aarontodd82/GenesisEngine/src/GenesisEngine.cpp

#include "GenesisEngine.h"

// =============================================================================
// Timing Constants
// VGM sample rate is 44100 Hz
// Microseconds per sample = 1000000 / 44100 = 22.675736961...
//
// For integer math, we use: samples = (elapsed_micros * 441) / 10000
// This gives us exact timing with no floating point
// =============================================================================

// =============================================================================
// Constructor
// =============================================================================

GenesisEngine::GenesisEngine(GenesisBoard& board)
  : board_(board),
    parser_(board),
    state_(GenesisEngineState::STOPPED),
    looping_(false),
    currentSample_(0),
    waitSamples_(0),
    playbackStartTime_(0),
    samplesPlayed_(0)
{
  // PCM data for DAC playback is now handled dynamically by PCMDataBank
  // inside VGMParser - no pre-allocated buffer needed
}

// =============================================================================
// Playback Control
// =============================================================================

bool GenesisEngine::play(const uint8_t* data, size_t length) {
  // Stop any current playback
  stop();

  // Set up PROGMEM source
  progmemSource_.setData(data, length);

  if (!progmemSource_.open()) {
    GENESIS_DEBUG_PRINTLN("Failed to open PROGMEM source");
    return false;
  }

  parser_.setSource(&progmemSource_);

  bool success = startPlayback();

  // After parsing header, set data start offset so seek positions are relative
  if (success) {
    progmemSource_.setDataStart(parser_.getDataOffset());
  }

  return success;
}

bool GenesisEngine::playChunked(const uint8_t* const* chunks, const uint16_t* chunkSizes,
                                 uint8_t numChunks, uint32_t totalLength) {
  // Stop any current playback
  stop();

  // Set up chunked PROGMEM source
  chunkedProgmemSource_.setData(chunks, chunkSizes, numChunks, totalLength);

  if (!chunkedProgmemSource_.open()) {
    GENESIS_DEBUG_PRINTLN("Failed to open chunked PROGMEM source");
    return false;
  }

  parser_.setSource(&chunkedProgmemSource_);

  bool success = startPlayback();

  // After parsing header, set data start offset so seek positions are relative
  if (success) {
    chunkedProgmemSource_.setDataStart(parser_.getDataOffset());
  }

  return success;
}

bool GenesisEngine::startPlayback() {
  // Parse header
  if (!parser_.parseHeader()) {
    GENESIS_DEBUG_PRINTLN("Failed to parse VGM header");
    state_ = GenesisEngineState::STOPPED;
    return false;
  }

  // Reset timing
  currentSample_ = 0;
  waitSamples_ = 0;
  samplesPlayed_ = 0;
  playbackStartTime_ = micros();

  // Reset hardware
  board_.muteAll();

  // Start playing
  state_ = GenesisEngineState::PLAYING;

  GENESIS_DEBUG_PRINTLN("Playback started");
  return true;
}

void GenesisEngine::stop() {
  if (state_ == GenesisEngineState::STOPPED) {
    return;
  }

  // Full hardware reset to clear any hanging notes
  board_.reset();

  // Reset state
  parser_.reset();
  state_ = GenesisEngineState::STOPPED;
  currentSample_ = 0;
  waitSamples_ = 0;

  GENESIS_DEBUG_PRINTLN("Playback stopped");
}

void GenesisEngine::pause() {
  if (state_ == GenesisEngineState::PLAYING) {
    state_ = GenesisEngineState::PAUSED;
    board_.muteAll();
    GENESIS_DEBUG_PRINTLN("Playback paused");
  }
}

void GenesisEngine::resume() {
  if (state_ == GenesisEngineState::PAUSED) {
    state_ = GenesisEngineState::PLAYING;
    // Adjust start time so timing continues correctly
    // We pretend playback started (now - time_already_played)
    uint32_t elapsedSamplesMicros = (samplesPlayed_ * 10000UL) / 441UL;
    playbackStartTime_ = micros() - elapsedSamplesMicros;
    GENESIS_DEBUG_PRINTLN("Playback resumed");
  }
}

// =============================================================================
// Update
// =============================================================================

void GenesisEngine::update() {
  if (state_ != GenesisEngineState::PLAYING) {
    return;
  }

  uint32_t now = micros();
  uint32_t elapsed = now - playbackStartTime_;

  // Handle micros() overflow (happens every ~70 minutes)
  // If elapsed is huge, assume overflow occurred
  if (elapsed > 0x80000000UL) {
    // Overflow - reset timing base
    playbackStartTime_ = now;
    elapsed = 0;
    // Keep samplesPlayed_ as-is to maintain position
  }

  // Calculate how many samples should have played by now
  // samples = elapsed_micros * 44100 / 1000000 = elapsed_micros * 441 / 10000
  uint32_t targetSamples = (elapsed / 10000UL) * 441UL + ((elapsed % 10000UL) * 441UL) / 10000UL;

  // Process commands until we catch up
  while (samplesPlayed_ < targetSamples) {
    // If we have pending wait samples, consume them
    if (waitSamples_ > 0) {
      uint32_t samplesToAdvance = targetSamples - samplesPlayed_;
      if (samplesToAdvance > waitSamples_) {
        samplesToAdvance = waitSamples_;
      }

      waitSamples_ -= samplesToAdvance;
      samplesPlayed_ += samplesToAdvance;
      currentSample_ += samplesToAdvance;

      if (waitSamples_ > 0) {
        // Still waiting, done for now
        return;
      }
    }

    // Process commands until next wait
    processCommands();

    if (state_ != GenesisEngineState::PLAYING) {
      // Playback ended
      return;
    }
  }
}

void GenesisEngine::processCommands() {
  // Process VGM commands until a wait is encountered
  waitSamples_ = parser_.processUntilWait();

  if (parser_.isFinished()) {
    // End of file reached
    if (looping_ && parser_.hasLoop()) {
      // Seek to loop point
      if (parser_.seekToLoop()) {
        GENESIS_DEBUG_PRINTLN("Looping");
        waitSamples_ = parser_.processUntilWait();
        return;
      }
    }

    // Playback finished - full reset to clear any hanging notes
    board_.reset();
    state_ = GenesisEngineState::FINISHED;
    GENESIS_DEBUG_PRINTLN("Playback finished");
  }
}

// =============================================================================
// SD Card Playback
// =============================================================================

#if GENESIS_ENGINE_USE_SD
bool GenesisEngine::playFile(const char* path) {
  // Stop any current playback
  stop();

  // Check file extension
  size_t len = strlen(path);
  bool isVGZ = false;
  if (len >= 4) {
    const char* ext = path + len - 4;
    isVGZ = (strcasecmp(ext, ".vgz") == 0);
  }

#if GENESIS_ENGINE_USE_VGZ
  // Use VGZSource for VGZ files (streaming decompression)
  if (isVGZ) {
    if (!vgzSource_.openFile(path)) {
      GENESIS_DEBUG_PRINT("Failed to open VGZ: ");
      GENESIS_DEBUG_PRINTLN(path);
      return false;
    }

    if (!vgzSource_.open()) {
      GENESIS_DEBUG_PRINTLN("Failed to prepare VGZ source");
      return false;
    }

    parser_.setSource(&vgzSource_);
    bool success = startPlayback();

    // After parsing header, notify VGZSource that we've reached data start
    // This resets currentDataPos_ to 0, so positions are relative to data start
    if (success) {
      vgzSource_.setDataStart();

      // Set loop offset relative to data start (VGMParser now calculates this)
      if (parser_.hasLoop()) {
        vgzSource_.setLoopOffset(parser_.getLoopOffsetInData());
      }
    }

    return success;
  }
#else
  // VGZ not supported on this platform
  if (isVGZ) {
    Serial.println("VGZ files not supported on this platform");
    Serial.println("Use vgm_prep.py to convert:");
    Serial.println("  python vgm_prep.py song.vgz -o song.vgm");
    return false;
  }
#endif

  // Use SDSource for VGM files (direct streaming)
  if (!sdSource_.openFile(path)) {
    GENESIS_DEBUG_PRINT("Failed to open: ");
    GENESIS_DEBUG_PRINTLN(path);
    return false;
  }

  if (!sdSource_.open()) {
    GENESIS_DEBUG_PRINTLN("Failed to prepare SD source");
    return false;
  }

  parser_.setSource(&sdSource_);
  bool success = startPlayback();

  // After parsing header, set data start offset so seek positions are relative
  if (success) {
    sdSource_.setDataStart(parser_.getDataOffset());
  }

  return success;
}
#endif // GENESIS_ENGINE_USE_SD
