aarontodd82/GenesisEngine/examples/MIDISynth/MIDISynth.ino

/**
 * MIDISynth - MIDI Synthesizer for GenesisEngine
 *
 * Turns the GenesisEngine hardware into a MIDI synthesizer.
 *
 * MIDI Channel Mapping:
 *   Ch 1-6:  YM2612 FM channels 1-6
 *   Ch 7-9:  SN76489 PSG tone channels 1-3
 *   Ch 10:   SN76489 PSG noise channel
 *
 * Supported Platforms:
 *   - Teensy 4.x: USB MIDI (set USB Type to "Serial + MIDI")
 *   - Arduino Uno/Mega: Serial MIDI via companion app
 *   - Any board: Serial MIDI at 115200 baud
 *
 * Both USB MIDI and Serial MIDI can be used simultaneously on Teensy.
 */

// =============================================================================
// Platform Detection
// =============================================================================

// Detect if USB MIDI is available (Teensy with MIDI enabled)
#if defined(USBCON) && defined(TEENSYDUINO)
    #define HAS_USB_MIDI 1
#else
    #define HAS_USB_MIDI 0
#endif

// Firmware version for identification
#define FIRMWARE_VERSION 1

#include <GenesisBoard.h>
#include <synth/FMPatch.h>
#include <synth/FMFrequency.h>
#include <synth/PSGFrequency.h>
#include <synth/PSGEnvelope.h>
#include <synth/DefaultPatches.h>

// =============================================================================
// Pin Configuration (platform specific)
// =============================================================================

#ifdef ARDUINO_ARCH_ESP32
  const uint8_t PIN_WR_P = 16;  // WR_P - SN76489 (PSG) write strobe
  const uint8_t PIN_WR_Y = 17;  // WR_Y - YM2612 write strobe
  const uint8_t PIN_IC_Y = 25;  // IC_Y - YM2612 reset
  const uint8_t PIN_A0_Y = 26;  // A0_Y - YM2612 address bit 0
  const uint8_t PIN_A1_Y = 27;  // A1_Y - YM2612 address bit 1 (port select)
  const uint8_t PIN_SCK  = 18;  // SCK  - Hardware SPI (fixed on ESP32)
  const uint8_t PIN_SDI  = 23;  // SDI  - Hardware SPI (fixed on ESP32)
#else
  // Teensy / Arduino defaults
  const uint8_t PIN_WR_P = 2;   // WR_P - SN76489 (PSG) write strobe
  const uint8_t PIN_WR_Y = 3;   // WR_Y - YM2612 write strobe
  const uint8_t PIN_IC_Y = 4;   // IC_Y - YM2612 reset
  const uint8_t PIN_A0_Y = 5;   // A0_Y - YM2612 address bit 0
  const uint8_t PIN_A1_Y = 6;   // A1_Y - YM2612 address bit 1 (port select)
  const uint8_t PIN_SCK  = 13;  // SCK  - Shift register clock (ignored w/ HW SPI)
  const uint8_t PIN_SDI  = 11;  // SDI  - Shift register data (ignored w/ HW SPI)
#endif

GenesisBoard board(PIN_WR_P, PIN_WR_Y, PIN_IC_Y, PIN_A0_Y, PIN_A1_Y, PIN_SCK, PIN_SDI);

// =============================================================================
// Patch Storage
// =============================================================================

// RAM storage for user-loaded patches
FMPatch fmPatches[16];           // 16 FM patch slots
PSGEnvelope psgEnvelopes[8];     // 8 PSG envelope slots

// Current patch assignment per channel
uint8_t fmChannelPatch[6] = {0, 1, 2, 3, 4, 5};
uint8_t psgChannelEnv[4] = {0, 1, 2, 3};  // Each PSG channel gets different envelope

// =============================================================================
// PSG Envelope State (software envelopes at 60Hz)
// =============================================================================

struct PSGChannelState {
    bool active;
    bool noteOn;
    uint8_t envPos;
    uint16_t baseTone;
    uint8_t baseNote;
};

PSGChannelState psgState[4] = {0};

// =============================================================================
// Synth Mode
// =============================================================================

enum SynthMode {
    MODE_MULTI,      // 6 independent FM channels (Ch 1-6), each with own patch
    MODE_POLY6       // 6-voice polyphonic on Ch 1, all same patch
};

SynthMode synthMode = MODE_MULTI;
uint8_t polyPatchSlot = 0;  // Patch slot used in poly mode

// =============================================================================
// FM Channel/Voice State
// =============================================================================

struct FMChannelState {
    bool noteOn;
    bool sustainPending;  // Note should release when sustain pedal is lifted
    uint8_t currentNote;
    uint8_t velocity;
    uint32_t timestamp;  // For voice stealing (when note started)
};

FMChannelState fmState[6] = {0};

// Sustain pedal state per channel (for multi mode) or global (for poly mode)
bool sustainPedal[16] = {false};

// Pitch bend per FM channel (-8192 to +8191)
// In poly mode, all voices share the pitch bend from channel 0
int16_t fmPitchBend[6] = {0, 0, 0, 0, 0, 0};

// =============================================================================
// Timing
// =============================================================================

uint32_t lastEnvTick = 0;
const uint32_t ENV_TICK_US = 16667;  // 60Hz = 16667 microseconds

// =============================================================================
// Forward Declarations
// =============================================================================

void setFMFrequencyWithBend(uint8_t ch, uint8_t note, int16_t bend);
void fmNoteOn(uint8_t ch, uint8_t note, uint8_t velocity);
void fmNoteOff(uint8_t ch, uint8_t note);
void fmKeyOff(uint8_t ch);
void writeFMPatch(uint8_t ch, const FMPatch& patch);
void processSerialMIDI();
void handleSerialMIDIByte(uint8_t byte);

// =============================================================================
// Serial MIDI Parser State
// =============================================================================

// MIDI message types for parsing
#define MIDI_NOTE_OFF       0x80
#define MIDI_NOTE_ON        0x90
#define MIDI_POLY_PRESSURE  0xA0
#define MIDI_CONTROL_CHANGE 0xB0
#define MIDI_PROGRAM_CHANGE 0xC0
#define MIDI_CHAN_PRESSURE  0xD0
#define MIDI_PITCH_BEND     0xE0
#define MIDI_SYSEX_START    0xF0
#define MIDI_SYSEX_END      0xF7

// Serial MIDI parser state
uint8_t serialMidiBuffer[128];   // Buffer for incoming MIDI data
uint8_t serialMidiPos = 0;       // Current position in buffer
uint8_t serialMidiExpected = 0;  // Expected message length
uint8_t serialMidiStatus = 0;    // Running status byte
bool serialInSysEx = false;      // Currently receiving SysEx

// =============================================================================
// Voice Allocator (for Poly Mode)
// =============================================================================

/**
 * Find a voice to use for a new note.
 * Strategy:
 *   1. Reuse voice if same note is retriggered
 *   2. Use first free voice
 *   3. Steal oldest voice (voice stealing)
 */
int8_t allocateVoice(uint8_t note) {
    // 1. Check if this note is already playing (retrigger - reuse same voice)
    for (int i = 0; i < 6; i++) {
        if (fmState[i].noteOn && fmState[i].currentNote == note) {
            return i;
        }
    }

    // 2. Find first free voice
    for (int i = 0; i < 6; i++) {
        if (!fmState[i].noteOn) {
            return i;
        }
    }

    // 3. All voices busy - steal oldest note
    uint32_t oldest = UINT32_MAX;
    int8_t oldestIdx = 0;
    for (int i = 0; i < 6; i++) {
        if (fmState[i].timestamp < oldest) {
            oldest = fmState[i].timestamp;
            oldestIdx = i;
        }
    }

    // Release the stolen voice before reusing
    fmKeyOff(oldestIdx);

    return oldestIdx;
}

/**
 * Find the voice playing a specific note (for note-off).
 * If multiple voices play same note, returns the oldest one (FIFO release).
 * Returns -1 if note not found.
 */
int8_t findVoiceByNote(uint8_t note) {
    int8_t found = -1;
    uint32_t oldest = UINT32_MAX;

    for (int i = 0; i < 6; i++) {
        if (fmState[i].noteOn && fmState[i].currentNote == note) {
            if (fmState[i].timestamp < oldest) {
                oldest = fmState[i].timestamp;
                found = i;
            }
        }
    }
    return found;
}

/**
 * Switch to poly mode - load same patch on all 6 FM channels
 */
void enablePolyMode(uint8_t patchSlot) {
    synthMode = MODE_POLY6;
    polyPatchSlot = patchSlot;

    // Load the same patch on all 6 channels
    for (uint8_t ch = 0; ch < 6; ch++) {
        fmChannelPatch[ch] = patchSlot;  // All channels use same patch
        writeFMPatch(ch, fmPatches[patchSlot]);
        fmState[ch].noteOn = false;
    }

    Serial.print("Poly mode enabled, patch slot ");
    Serial.println(patchSlot);
}

/**
 * Switch to multi-timbral mode - restore individual patches per channel
 */
void enableMultiMode() {
    synthMode = MODE_MULTI;

    // Restore individual patches per channel
    for (uint8_t ch = 0; ch < 6; ch++) {
        writeFMPatch(ch, fmPatches[fmChannelPatch[ch]]);
        fmState[ch].noteOn = false;
    }

    Serial.println("Multi mode enabled");
}

// =============================================================================
// Setup
// =============================================================================

void setup() {
    Serial.begin(115200);

    board.begin();
    board.reset();

    // Load default patches from PROGMEM
    loadDefaultPatches();

    // Initialize all FM channels with their assigned patches
    for (uint8_t ch = 0; ch < 6; ch++) {
        writeFMPatch(ch, fmPatches[fmChannelPatch[ch]]);
        // Set stereo output (both L+R enabled)
        setFMPanning(ch, 0xC0);  // Both speakers
    }

    // Silence PSG
    board.silencePSG();

    Serial.println("MIDISynth ready");
}

// =============================================================================
// Main Loop
// =============================================================================

void loop() {
    // Process USB MIDI from computer (Teensy only)
    #if HAS_USB_MIDI
    while (usbMIDI.read()) {
        // Convert usbMIDI type to our unified type constants
        uint8_t type = usbMIDI.getType();
        uint8_t unifiedType;
        switch (type) {
            case usbMIDI.NoteOff:         unifiedType = TYPE_NOTE_OFF; break;
            case usbMIDI.NoteOn:          unifiedType = TYPE_NOTE_ON; break;
            case usbMIDI.ControlChange:   unifiedType = TYPE_CONTROL_CHANGE; break;
            case usbMIDI.ProgramChange:   unifiedType = TYPE_PROGRAM_CHANGE; break;
            case usbMIDI.PitchBend:       unifiedType = TYPE_PITCH_BEND; break;
            case usbMIDI.SystemExclusive: unifiedType = TYPE_SYSEX; break;
            default: continue;  // Skip unknown types
        }
        handleMIDI(
            unifiedType,
            usbMIDI.getChannel() - 1,  // Convert to 0-indexed
            usbMIDI.getData1(),
            usbMIDI.getData2(),
            usbMIDI.getSysExArray(),
            usbMIDI.getSysExArrayLength()
        );
    }
    #endif

    // Process Serial MIDI (all platforms - from companion app)
    processSerialMIDI();

    // Update PSG envelopes at 60Hz
    uint32_t now = micros();
    if (now - lastEnvTick >= ENV_TICK_US) {
        lastEnvTick += ENV_TICK_US;
        updatePSGEnvelopes();
    }
}

// =============================================================================
// MIDI Handler (unified for USB and Serial MIDI)
// =============================================================================

// MIDI type constants (compatible with both usbMIDI and serial parsing)
#define TYPE_NOTE_OFF       0x08
#define TYPE_NOTE_ON        0x09
#define TYPE_POLY_PRESSURE  0x0A
#define TYPE_CONTROL_CHANGE 0x0B
#define TYPE_PROGRAM_CHANGE 0x0C
#define TYPE_CHAN_PRESSURE  0x0D
#define TYPE_PITCH_BEND     0x0E
#define TYPE_SYSEX          0x0F

void handleMIDI(uint8_t type, uint8_t channel, uint8_t d1, uint8_t d2,
                const uint8_t* sysex, uint16_t sysexLen) {

    // Channel is 0-indexed here (convert from 1-indexed if needed by caller)
    uint8_t ch = channel;

    switch (type) {
        case TYPE_NOTE_ON:
            if (d2 > 0) {
                noteOn(ch, d1, d2);
            } else {
                noteOff(ch, d1);
            }
            break;

        case TYPE_NOTE_OFF:
            noteOff(ch, d1);
            break;

        case TYPE_CONTROL_CHANGE:
            handleCC(ch, d1, d2);
            break;

        case TYPE_PROGRAM_CHANGE:
            handleProgramChange(ch, d1);
            break;

        case TYPE_PITCH_BEND:
            handlePitchBend(ch, (d2 << 7) | d1);
            break;

        case TYPE_SYSEX:
            if (sysex && sysexLen > 0) {
                handleSysEx(sysex, sysexLen);
            }
            break;
    }
}

// =============================================================================
// Note On/Off
// =============================================================================

void noteOn(uint8_t midiCh, uint8_t note, uint8_t velocity) {
    if (synthMode == MODE_POLY6) {
        // Poly mode: MIDI Ch 1 controls all 6 FM voices
        if (midiCh == 0) {
            int8_t voice = allocateVoice(note);
            if (voice >= 0) {
                fmNoteOn(voice, note, velocity);
            }
        } else if (midiCh >= 6 && midiCh < 9) {
            // PSG still works on Ch 7-9
            psgNoteOn(midiCh - 6, note, velocity);
        } else if (midiCh == 9) {
            psgNoiseOn(note, velocity);
        }
    } else {
        // Multi mode: Ch 1-6 = FM 1-6, Ch 7-9 = PSG, Ch 10 = Noise
        if (midiCh < 6) {
            fmNoteOn(midiCh, note, velocity);
        } else if (midiCh < 9) {
            psgNoteOn(midiCh - 6, note, velocity);
        } else if (midiCh == 9) {
            psgNoiseOn(note, velocity);
        }
    }
}

void noteOff(uint8_t midiCh, uint8_t note) {
    if (synthMode == MODE_POLY6) {
        // Poly mode: find which voice is playing this note
        if (midiCh == 0) {
            int8_t voice = findVoiceByNote(note);
            if (voice >= 0) {
                fmNoteOff(voice, note);
            }
        } else if (midiCh >= 6 && midiCh < 9) {
            psgNoteOff(midiCh - 6);
        } else if (midiCh == 9) {
            psgNoiseOff();
        }
    } else {
        // Multi mode
        if (midiCh < 6) {
            fmNoteOff(midiCh, note);
        } else if (midiCh < 9) {
            psgNoteOff(midiCh - 6);
        } else if (midiCh == 9) {
            psgNoiseOff();
        }
    }
}

// =============================================================================
// FM Functions
// =============================================================================

void fmNoteOn(uint8_t ch, uint8_t note, uint8_t velocity) {
    // Store state
    fmState[ch].noteOn = true;
    fmState[ch].currentNote = note;
    fmState[ch].velocity = velocity;
    fmState[ch].timestamp = millis();  // For voice stealing

    // Apply velocity to carrier TL (simple scaling)
    applyVelocity(ch, velocity);

    // Set frequency (apply any active pitch bend)
    // In poly mode, use channel 0's pitch bend for all voices
    int16_t bend = (synthMode == MODE_POLY6) ? fmPitchBend[0] : fmPitchBend[ch];
    if (bend != 0) {
        setFMFrequencyWithBend(ch, note, bend);
    } else {
        setFMFrequency(ch, note);
    }

    // Key on (all 4 operators)
    fmKeyOn(ch);
}

void fmNoteOff(uint8_t ch, uint8_t note) {
    // Only release if this is the note that's playing
    if (fmState[ch].noteOn && fmState[ch].currentNote == note) {
        // Check sustain pedal - in poly mode use ch 0, in multi mode use the actual channel
        uint8_t sustainCh = (synthMode == MODE_POLY6) ? 0 : ch;
        if (sustainPedal[sustainCh]) {
            // Mark as pending release instead of actually releasing
            fmState[ch].sustainPending = true;
        } else {
            fmState[ch].noteOn = false;
            fmState[ch].sustainPending = false;
            fmKeyOff(ch);
        }
    }
}

void fmKeyOn(uint8_t ch) {
    FMFrequency::keyOn(board, ch);
}

void fmKeyOff(uint8_t ch) {
    FMFrequency::keyOff(board, ch);
}

void setFMFrequency(uint8_t ch, uint8_t note) {
    FMFrequency::writeToChannel(board, ch, note);
}

void setFMPanning(uint8_t ch, uint8_t pan) {
    uint8_t port = (ch >= 3) ? 1 : 0;
    uint8_t chReg = ch % 3;

    // Register B4-B6: L/R/AMS/PMS
    // We preserve AMS/PMS and just set L/R bits
    board.writeYM2612(port, 0xB4 + chReg, pan);
}

// Helper: get carrier mask for algorithm - delegates to library
void getCarrierMask(uint8_t algorithm, bool* isCarrier) {
    FMPatchUtils::getCarrierMask(algorithm, isCarrier);
}

void applyVelocity(uint8_t ch, uint8_t velocity) {
    // Scale carrier TL based on velocity
    // TL 0 = loudest, 127 = silent
    // Velocity 127 = loudest, 0 = silent

    FMPatch& patch = fmPatches[fmChannelPatch[ch]];
    bool isCarrier[4];
    getCarrierMask(patch.algorithm, isCarrier);

    // Calculate velocity attenuation (0 = none, ~40 = significant)
    uint8_t attenuation = (127 - velocity) / 3;

    uint8_t port = (ch >= 3) ? 1 : 0;
    uint8_t chReg = ch % 3;

    // Operator register offsets: S1=0, S3=8, S2=4, S4=12
    const uint8_t opOffsets[4] = {0, 8, 4, 12};

    for (int op = 0; op < 4; op++) {
        if (isCarrier[op]) {
            uint8_t tl = patch.op[op].tl;
            tl = min(127, tl + attenuation);
            board.writeYM2612(port, 0x40 + opOffsets[op] + chReg, tl);
        }
    }
}

void applyVolumeAttenuation(uint8_t ch, const FMPatch& patch, uint8_t attenuation) {
    // Apply attenuation to carrier operators
    bool isCarrier[4];
    getCarrierMask(patch.algorithm, isCarrier);

    uint8_t port = (ch >= 3) ? 1 : 0;
    uint8_t chReg = ch % 3;
    const uint8_t opOffsets[4] = {0, 8, 4, 12};

    for (int op = 0; op < 4; op++) {
        if (isCarrier[op]) {
            uint8_t tl = patch.op[op].tl;
            tl = min(127, tl + attenuation);
            board.writeYM2612(port, 0x40 + opOffsets[op] + chReg, tl);
        }
    }
}

// =============================================================================
// PSG Functions
// =============================================================================

void psgNoteOn(uint8_t ch, uint8_t note, uint8_t velocity) {
    if (ch >= 3) return;

    // Set frequency
    uint16_t tone = pgm_read_word(&psgToneTable[note]);
    psgState[ch].baseTone = tone;
    psgState[ch].baseNote = note;

    // Write tone
    board.writePSG(0x80 | (ch << 5) | (tone & 0x0F));
    board.writePSG((tone >> 4) & 0x3F);

    // Start envelope
    psgState[ch].active = true;
    psgState[ch].noteOn = true;
    psgState[ch].envPos = 0;

    // Set initial volume (envelope will take over)
    uint8_t vol = 15 - (velocity >> 3);  // 0-15, 0=loud
    board.writePSG(0x90 | (ch << 5) | vol);
}

void psgNoteOff(uint8_t ch) {
    if (ch >= 3) return;

    psgState[ch].noteOn = false;
    // Let envelope finish or silence immediately
    board.writePSG(0x90 | (ch << 5) | 0x0F);  // Silence
    psgState[ch].active = false;
}

void psgNoiseOn(uint8_t note, uint8_t velocity) {
    // Noise mode based on note
    // Low notes = periodic noise, high notes = white noise
    uint8_t mode = (note < 64) ? 0x00 : 0x04;  // Bit 2 = white noise
    uint8_t freq = note % 4;  // 0-3 frequency select

    board.writePSG(0xE0 | mode | freq);

    // Set volume
    uint8_t vol = 15 - (velocity >> 3);
    board.writePSG(0xF0 | vol);

    psgState[3].active = true;
    psgState[3].noteOn = true;
}

void psgNoiseOff() {
    board.writePSG(0xFF);  // Silence noise channel
    psgState[3].active = false;
    psgState[3].noteOn = false;
}

// =============================================================================
// PSG Envelope Processing (called at 60Hz)
// =============================================================================

void updatePSGEnvelopes() {
    for (uint8_t ch = 0; ch < 3; ch++) {
        if (!psgState[ch].active) continue;

        PSGEnvelope& env = psgEnvelopes[psgChannelEnv[ch]];

        if (psgState[ch].envPos >= env.length) {
            // Envelope finished
            if (!psgState[ch].noteOn) {
                psgState[ch].active = false;
                board.writePSG(0x90 | (ch << 5) | 0x0F);  // Silence
            }
            continue;
        }

        uint8_t data = env.data[psgState[ch].envPos];
        uint8_t volume = data & 0x0F;

        // Apply volume
        board.writePSG(0x90 | (ch << 5) | volume);

        // Advance position
        psgState[ch].envPos++;

        // Handle loop
        if (psgState[ch].envPos >= env.length && env.loopStart != 0xFF) {
            psgState[ch].envPos = env.loopStart;
        }
    }
}

// =============================================================================
// Control Change Handler
// =============================================================================

// LFO enabled state
bool lfoEnabled = false;

/**
 * Echo a CC to serial so companion app can update its UI
 * This ensures the app always reflects the actual hardware state
 */
void echoCC(uint8_t ch, uint8_t cc, uint8_t value) {
    Serial.write(0xB0 | (ch & 0x0F));
    Serial.write(cc & 0x7F);
    Serial.write(value & 0x7F);
}

void handleCC(uint8_t ch, uint8_t cc, uint8_t value) {
    // Mode switching CCs work on any channel
    switch (cc) {
        case 126:  // Mono mode (MIDI standard) - we use for Multi-timbral
            enableMultiMode();
            return;

        case 127:  // Poly mode (MIDI standard)
            // In poly mode, use Program Change value as patch slot
            // Default to slot 0 if not set
            enablePolyMode(polyPatchSlot);
            return;
    }

    // In poly mode, only respond to MIDI Ch 1 for FM controls
    if (synthMode == MODE_POLY6 && ch != 0 && ch < 6) {
        return;  // Ignore FM CCs on channels 2-6 in poly mode
    }

    if (ch >= 6) return;  // Only FM channels for CCs below

    switch (cc) {
        case 1:  // Mod wheel - LFO depth (vibrato)
            {
                // Enable LFO if mod wheel > 0
                if (value > 0 && !lfoEnabled) {
                    // Enable LFO at medium speed (freq index 4 ≈ 5.9 Hz)
                    board.writeYM2612(0, 0x22, 0x08 | 4);
                    lfoEnabled = true;
                } else if (value == 0 && lfoEnabled) {
                    // Disable LFO
                    board.writeYM2612(0, 0x22, 0x00);
                    lfoEnabled = false;
                }

                // Set PMS (Phase Modulation Sensitivity) based on value
                uint8_t pms = value >> 4;  // 0-7 from 0-127

                if (synthMode == MODE_POLY6) {
                    // Apply to all 6 channels in poly mode
                    for (uint8_t i = 0; i < 6; i++) {
                        uint8_t port = (i >= 3) ? 1 : 0;
                        uint8_t chReg = i % 3;
                        board.writeYM2612(port, 0xB4 + chReg, 0xC0 | pms);
                    }
                } else {
                    uint8_t port = (ch >= 3) ? 1 : 0;
                    uint8_t chReg = ch % 3;
                    board.writeYM2612(port, 0xB4 + chReg, 0xC0 | pms);
                }
                echoCC(ch, cc, value);
            }
            break;

        case 7:  // Volume - scale carrier TLs
            {
                uint8_t attenuation = (127 - value);

                if (synthMode == MODE_POLY6) {
                    // Apply to all 6 channels in poly mode
                    FMPatch& patch = fmPatches[polyPatchSlot];
                    for (uint8_t i = 0; i < 6; i++) {
                        applyVolumeAttenuation(i, patch, attenuation);
                    }
                } else {
                    FMPatch& patch = fmPatches[fmChannelPatch[ch]];
                    applyVolumeAttenuation(ch, patch, attenuation);
                }
                echoCC(ch, cc, value);
            }
            break;

        case 10: // Pan
            {
                uint8_t pan;
                if (value < 32) pan = 0x80;       // Left only
                else if (value > 96) pan = 0x40; // Right only
                else pan = 0xC0;                  // Center (both)
                setFMPanning(ch, pan);
                echoCC(ch, cc, value);
            }
            break;

        case 14: // Algorithm (GenMDM-style)
            if (value < 8) {
                fmPatches[fmChannelPatch[ch]].algorithm = value;
                writeFMPatch(ch, fmPatches[fmChannelPatch[ch]]);
                echoCC(ch, cc, value);
            }
            break;

        case 15: // Feedback
            if (value < 8) {
                fmPatches[fmChannelPatch[ch]].feedback = value;
                writeFMPatch(ch, fmPatches[fmChannelPatch[ch]]);
                echoCC(ch, cc, value);
            }
            break;

        // TL for operators 1-4 (CC 16-19)
        case 16: case 17: case 18: case 19:
            {
                uint8_t op = cc - 16;
                fmPatches[fmChannelPatch[ch]].op[op].tl = value;
                writeOperatorTL(ch, op, value);
                echoCC(ch, cc, value);
            }
            break;

        case 64:  // Sustain pedal
            handleSustainPedal(ch, value >= 64);
            echoCC(ch, cc, value);
            break;

        case 120: // All Sound Off - immediately silence
            allSoundOff(ch);
            break;

        case 123: // All Notes Off - release all held notes
            allNotesOff(ch);
            break;
    }
}

void writeOperatorTL(uint8_t ch, uint8_t op, uint8_t tl) {
    uint8_t port = (ch >= 3) ? 1 : 0;
    uint8_t chReg = ch % 3;
    const uint8_t opOffsets[4] = {0, 8, 4, 12};
    board.writeYM2612(port, 0x40 + opOffsets[op] + chReg, tl);
}

// =============================================================================
// Sustain Pedal & Panic Functions
// =============================================================================

void handleSustainPedal(uint8_t ch, bool on) {
    sustainPedal[ch] = on;

    if (!on) {
        // Pedal released - release any notes marked as sustainPending
        if (synthMode == MODE_POLY6 && ch == 0) {
            // In poly mode, sustain on ch 0 affects all 6 voices
            for (uint8_t i = 0; i < 6; i++) {
                if (fmState[i].sustainPending) {
                    fmState[i].noteOn = false;
                    fmState[i].sustainPending = false;
                    fmKeyOff(i);
                }
            }
        } else if (synthMode == MODE_MULTI && ch < 6) {
            // In multi mode, each FM channel has its own sustain
            if (fmState[ch].sustainPending) {
                fmState[ch].noteOn = false;
                fmState[ch].sustainPending = false;
                fmKeyOff(ch);
            }
        }
        // PSG doesn't support sustain pedal
    }
}

void allNotesOff(uint8_t ch) {
    // Release all notes on this channel (or all channels if ch >= 16)
    if (ch < 6 || ch >= 16) {
        // FM channels
        uint8_t start = (ch >= 16) ? 0 : ch;
        uint8_t end = (ch >= 16) ? 6 : ch + 1;
        for (uint8_t i = start; i < end; i++) {
            if (fmState[i].noteOn) {
                fmState[i].noteOn = false;
                fmState[i].sustainPending = false;
                fmKeyOff(i);
            }
        }
    }

    if ((ch >= 6 && ch < 10) || ch >= 16) {
        // PSG channels
        uint8_t start = (ch >= 16) ? 0 : ch - 6;
        uint8_t end = (ch >= 16) ? 3 : start + 1;
        for (uint8_t i = start; i < end; i++) {
            psgNoteOff(i);
        }
        if (ch == 9 || ch >= 16) {
            psgNoiseOff();
        }
    }
}

void allSoundOff(uint8_t ch) {
    // Immediately silence - same as allNotesOff but more aggressive
    // Could also reset controllers, but for now just do notes off
    allNotesOff(ch);

    // Additionally mute FM TL to max attenuation for immediate silence
    if (ch < 6 || ch >= 16) {
        uint8_t start = (ch >= 16) ? 0 : ch;
        uint8_t end = (ch >= 16) ? 6 : ch + 1;
        for (uint8_t i = start; i < end; i++) {
            // Set all operator TLs to max attenuation (127 = silent)
            for (uint8_t op = 0; op < 4; op++) {
                writeOperatorTL(i, op, 127);
            }
        }
    }

    if ((ch >= 6 && ch < 10) || ch >= 16) {
        // PSG - set to max attenuation (15 = silent)
        uint8_t start = (ch >= 16) ? 0 : ch - 6;
        uint8_t end = (ch >= 16) ? 3 : start + 1;
        for (uint8_t i = start; i < end; i++) {
            board.writePSG(0x90 | (i << 5) | 0x0F);
        }
        if (ch == 9 || ch >= 16) {
            board.writePSG(0x90 | (3 << 5) | 0x0F);  // Noise channel
        }
    }
}

// =============================================================================
// Program Change Handler
// =============================================================================

void handleProgramChange(uint8_t ch, uint8_t program) {
    if (synthMode == MODE_POLY6) {
        // In poly mode, Ch 1 Program Change sets patch for all 6 voices
        if (ch == 0 && program < 16) {
            polyPatchSlot = program;
            for (uint8_t i = 0; i < 6; i++) {
                writeFMPatch(i, fmPatches[program]);
            }
            Serial.print("Poly patch changed to slot ");
            Serial.println(program);
        } else if (ch >= 6 && ch < 10) {
            // PSG still works
            uint8_t psgCh = ch - 6;
            if (program < 8) {
                psgChannelEnv[psgCh] = program;
            }
        }
    } else {
        // Multi mode: each channel has its own patch
        if (ch < 6) {
            if (program < 16) {
                fmChannelPatch[ch] = program;
                writeFMPatch(ch, fmPatches[program]);
            }
        } else if (ch < 10) {
            uint8_t psgCh = ch - 6;
            if (program < 8) {
                psgChannelEnv[psgCh] = program;
            }
        }
    }
}

// =============================================================================
// Pitch Bend Handler
// =============================================================================

void handlePitchBend(uint8_t ch, uint16_t bend) {
    // bend: 0-16383, center = 8192
    // Convert to signed: -8192 to +8191
    int16_t bendOffset = (int16_t)bend - 8192;

    if (synthMode == MODE_POLY6) {
        // In poly mode, Ch 1 pitch bend affects all 6 voices
        if (ch != 0) return;

        fmPitchBend[0] = bendOffset;

        // Update all active voices
        for (uint8_t i = 0; i < 6; i++) {
            if (fmState[i].noteOn) {
                setFMFrequencyWithBend(i, fmState[i].currentNote, bendOffset);
            }
        }
    } else {
        // Multi mode: each channel has its own pitch bend
        if (ch >= 6) return;

        fmPitchBend[ch] = bendOffset;

        if (fmState[ch].noteOn) {
            setFMFrequencyWithBend(ch, fmState[ch].currentNote, bendOffset);
        }
    }
}

void setFMFrequencyWithBend(uint8_t ch, uint8_t note, int16_t bend) {
    FMFrequency::writeToChannelWithBend(board, ch, note, bend);
}

// =============================================================================
// SysEx Handler
// =============================================================================

// SysEx format: F0 7D 00 <cmd> <data...> F7
// Commands (Host -> Device):
//   0x01 = Load FM patch to channel: <channel> <42 bytes>
//   0x02 = Load PSG envelope: <channel> <length> <loopStart> <data...>
//   0x03 = Store FM patch to slot: <slot> <42 bytes>
//   0x04 = Recall FM patch to channel: <channel> <slot>
//   0x10 = Request patch dump: <slot>
//   0x11 = Request all patches
//   0x12 = Set synth mode: <mode> (0=Multi, 1=Poly)
//   0x13 = Ping/identify
//
// Responses (Device -> Host):
//   0x80 = Patch dump: <slot> <42 bytes>
//   0x81 = Identity: <mode> <version>

void sendSysExResponse(uint8_t cmd, const uint8_t* data, uint8_t len) {
    Serial.write(0xF0);
    Serial.write(0x7D);
    Serial.write(0x00);
    Serial.write(cmd);
    for (uint8_t i = 0; i < len; i++) {
        Serial.write(data[i]);
    }
    Serial.write(0xF7);
}

void sendPatchDump(uint8_t slot) {
    if (slot >= 16) return;

    uint8_t data[46];  // slot + 45 bytes extended patch
    data[0] = slot;

    // Serialize patch to extended format (45 bytes)
    const FMPatch& patch = fmPatches[slot];
    data[1] = patch.algorithm;
    data[2] = patch.feedback;
    for (int op = 0; op < 4; op++) {
        int offset = 3 + op * 10;
        data[offset + 0] = patch.op[op].mul;
        data[offset + 1] = patch.op[op].dt;
        data[offset + 2] = patch.op[op].tl;
        data[offset + 3] = patch.op[op].rs;
        data[offset + 4] = patch.op[op].ar;
        data[offset + 5] = patch.op[op].dr;
        data[offset + 6] = patch.op[op].sr;
        data[offset + 7] = patch.op[op].rr;
        data[offset + 8] = patch.op[op].sl;
        data[offset + 9] = patch.op[op].ssg;
    }
    // Extended parameters
    data[43] = patch.pan;
    data[44] = patch.ams;
    data[45] = patch.pms;

    sendSysExResponse(0x80, data, 46);
}

void handleSysEx(const uint8_t* data, uint16_t len) {
    // Minimum: F0 7D 00 cmd F7 = 5 bytes
    if (len < 5) return;

    // Check manufacturer ID (0x7D = educational/development)
    if (data[1] != 0x7D) return;

    uint8_t cmd = data[3];

    switch (cmd) {
        case 0x01:  // Load FM patch to channel
            // Accept both legacy (42-byte) and extended (45-byte) formats
            if (len >= 5 + 1 + FM_PATCH_SIZE_LEGACY) {  // cmd + channel + patch
                uint8_t ch = data[4];
                if (ch < 6) {
                    bool extended = (len >= 5 + 1 + FM_PATCH_SIZE_EXTENDED);
                    parsePatchData(&data[5], fmPatches[fmChannelPatch[ch]], extended);
                    if (synthMode == MODE_POLY6) {
                        // In poly mode, update all 6 channels with the shared patch
                        for (uint8_t i = 0; i < 6; i++) {
                            writeFMPatch(i, fmPatches[fmChannelPatch[ch]]);
                        }
                    } else {
                        writeFMPatch(ch, fmPatches[fmChannelPatch[ch]]);
                    }
                }
            }
            break;

        case 0x02:  // Load PSG envelope
            if (len >= 5 + 3) {  // cmd + channel + length + loopStart
                uint8_t ch = data[4];
                uint8_t envLen = data[5];
                uint8_t loopStart = data[6];
                if (ch < 4 && envLen <= 64 && len >= 5 + 3 + envLen) {
                    PSGEnvelope& env = psgEnvelopes[psgChannelEnv[ch]];
                    env.length = envLen;
                    env.loopStart = loopStart;
                    memcpy(env.data, &data[7], envLen);
                }
            }
            break;

        case 0x03:  // Store FM patch to slot
            // Accept both legacy (42-byte) and extended (45-byte) formats
            if (len >= 5 + 1 + FM_PATCH_SIZE_LEGACY) {
                uint8_t slot = data[4];
                if (slot < 16) {
                    bool extended = (len >= 5 + 1 + FM_PATCH_SIZE_EXTENDED);
                    parsePatchData(&data[5], fmPatches[slot], extended);
                }
            }
            break;

        case 0x04:  // Recall FM patch to channel
            if (len >= 5 + 2) {
                uint8_t ch = data[4];
                uint8_t slot = data[5];
                if (ch < 6 && slot < 16) {
                    fmChannelPatch[ch] = slot;
                    writeFMPatch(ch, fmPatches[slot]);
                }
            }
            break;

        case 0x10:  // Request patch dump
            if (len >= 5 + 1) {
                uint8_t slot = data[4];
                sendPatchDump(slot);
            }
            break;

        case 0x11:  // Request all patches
            for (uint8_t i = 0; i < 16; i++) {
                sendPatchDump(i);
            }
            break;

        case 0x12:  // Set synth mode
            if (len >= 5 + 1) {
                uint8_t mode = data[4];
                if (mode == 0) {
                    enableMultiMode();
                } else {
                    enablePolyMode(polyPatchSlot);
                }
            }
            break;

        case 0x13:  // Ping/identify
            {
                uint8_t response[2];
                response[0] = (synthMode == MODE_POLY6) ? 1 : 0;
                response[1] = FIRMWARE_VERSION;
                sendSysExResponse(0x81, response, 2);
            }
            break;
    }
}

// =============================================================================
// Patch Loading
// =============================================================================

// Parse patch from SysEx data - delegates to library
void parsePatchData(const uint8_t* data, struct FMPatch& patch, bool extended) {
    FMPatchUtils::parseFromData(data, patch, extended);
}

// Legacy wrapper for backward compatibility
void parseTFIPatch(const uint8_t* data, FMPatch& patch) {
    parsePatchData(data, patch, false);
}

void writeFMPatch(uint8_t ch, const struct FMPatch& patch) {
    FMPatchUtils::loadToChannel(board, ch, patch);
}

void loadDefaultPatches() {
    // Load default FM patches from PROGMEM
    for (int i = 0; i < DEFAULT_FM_PATCH_COUNT && i < 16; i++) {
        memcpy_P(&fmPatches[i], &defaultFMPatches[i], sizeof(FMPatch));
    }

    // Load default PSG envelopes from PROGMEM
    for (int i = 0; i < DEFAULT_PSG_ENV_COUNT && i < 8; i++) {
        memcpy_P(&psgEnvelopes[i], &defaultPSGEnvelopes[i], sizeof(PSGEnvelope));
    }
}

// =============================================================================
// Serial MIDI Parser
// =============================================================================

// Get expected data byte count for a MIDI status byte
uint8_t getMIDIMessageLength(uint8_t status) {
    uint8_t type = status & 0xF0;
    switch (type) {
        case MIDI_NOTE_OFF:
        case MIDI_NOTE_ON:
        case MIDI_POLY_PRESSURE:
        case MIDI_CONTROL_CHANGE:
        case MIDI_PITCH_BEND:
            return 2;  // Two data bytes
        case MIDI_PROGRAM_CHANGE:
        case MIDI_CHAN_PRESSURE:
            return 1;  // One data byte
        default:
            return 0;  // System messages handled separately
    }
}

void processSerialMIDI() {
    while (Serial.available()) {
        uint8_t byte = Serial.read();
        handleSerialMIDIByte(byte);
    }
}

void handleSerialMIDIByte(uint8_t byte) {
    // Handle SysEx
    if (serialInSysEx) {
        if (byte == MIDI_SYSEX_END) {
            // End of SysEx - process it
            serialMidiBuffer[serialMidiPos++] = byte;
            handleMIDI(TYPE_SYSEX, 0, 0, 0, serialMidiBuffer, serialMidiPos);
            serialInSysEx = false;
            serialMidiPos = 0;
        } else if (byte >= 0x80) {
            // Unexpected status byte - abort SysEx
            serialInSysEx = false;
            serialMidiPos = 0;
            // Fall through to handle this as a new message
            if (byte != MIDI_SYSEX_START) {
                handleSerialMIDIByte(byte);  // Recursive call for new status
            }
        } else {
            // SysEx data byte
            if (serialMidiPos < sizeof(serialMidiBuffer)) {
                serialMidiBuffer[serialMidiPos++] = byte;
            }
        }
        return;
    }

    // Check for status byte (high bit set)
    if (byte >= 0x80) {
        if (byte == MIDI_SYSEX_START) {
            // Start of SysEx
            serialInSysEx = true;
            serialMidiPos = 0;
            serialMidiBuffer[serialMidiPos++] = byte;
            return;
        }

        if (byte >= 0xF0) {
            // System real-time or common messages - ignore most
            return;
        }

        // Channel voice message - store as running status
        serialMidiStatus = byte;
        serialMidiExpected = getMIDIMessageLength(byte);
        serialMidiPos = 0;
        return;
    }

    // Data byte
    if (serialMidiStatus == 0) {
        // No running status - ignore
        return;
    }

    // Store data byte
    serialMidiBuffer[serialMidiPos++] = byte;

    // Check if message is complete
    if (serialMidiPos >= serialMidiExpected) {
        // Process complete message
        uint8_t channel = serialMidiStatus & 0x0F;
        uint8_t d1 = serialMidiBuffer[0];
        uint8_t d2 = (serialMidiExpected > 1) ? serialMidiBuffer[1] : 0;

        // Convert status nibble to our type constants
        uint8_t unifiedType;
        switch (serialMidiStatus & 0xF0) {
            case MIDI_NOTE_OFF:       unifiedType = TYPE_NOTE_OFF; break;
            case MIDI_NOTE_ON:        unifiedType = TYPE_NOTE_ON; break;
            case MIDI_CONTROL_CHANGE: unifiedType = TYPE_CONTROL_CHANGE; break;
            case MIDI_PROGRAM_CHANGE: unifiedType = TYPE_PROGRAM_CHANGE; break;
            case MIDI_PITCH_BEND:     unifiedType = TYPE_PITCH_BEND; break;
            default: return;  // Unsupported type
        }

        handleMIDI(unifiedType, channel, d1, d2, nullptr, 0);

        // Reset for next message (keep running status)
        serialMidiPos = 0;
    }
}
